aramder/orc/firmware/src/can_address_bringup/main.cpp

// SPDX-License-Identifier: Apache-2.0
// Copyright (c) 2026 Aram Dergevorkian
// ORC firmware bring-up: configurable CAN node address
//
// NOT application firmware. Reads the 4-bit address-select bank (external
// 10k pulldown per bit, switch/jumper to 3V3, on GPIO0/1/2/3 -- matching the
// as-fabbed schematic's NODE_ID0..NODE_ID3 nets) and reports the resulting
// 0-15 node address continuously, so a bench check can walk all 16 switch
// combinations and confirm each one reads back correctly before trusting
// the scheme in the field.
//
// See firmware/lib/orc_can_addr/orc_can_addr.h for the pin pick and the
// GPIO2 strapping-pin-safety reasoning (short version: GPIO2 is a strapping
// pin, but Table 3-3 shows it's don't-care whenever GPIO9=1, which this
// board's I2C pull-up guarantees at every reset -- verified specifically
// because the board was already at fab when this was checked).
//
// Nothing here has been run against real hardware with the address-select
// switches actually wired -- compiles cleanly, ready to flash.

#include <Arduino.h>
#include "orc_can_addr.h"

void setup() {
  Serial.begin(115200);
  delay(1500);
  Serial.println();
  Serial.println("=== ORC bring-up: CAN node address read ===");
  Serial.println("Bring-up/verification sketch -- not application firmware.");
  Serial.printf("Address bits: bit0=GPIO%u  bit1=GPIO%u  bit2=GPIO%u  bit3=GPIO%u\n",
                kOrcCanAddrBit0Pin, kOrcCanAddrBit1Pin, kOrcCanAddrBit2Pin, kOrcCanAddrBit3Pin);
  Serial.println("Wiring assumed: external 10k pulldown to GND per bit, switch/jumper to "
                  "3V3 -- open=0, closed=1. Walk all 16 combinations on the bench and "
                  "confirm each reads back correctly before trusting this in the field.");

  orcInitCanAddrPins();
}

void loop() {
  orcPrintCanAddress();
  delay(1000);
}
